thib-s/quadripod_robot/3d/mg996_base/exports/legA.stl

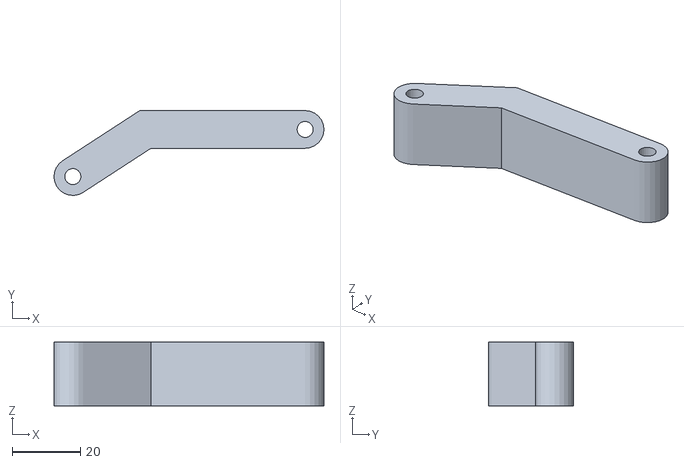
[picture p16: CAD file, 2018-07-05]
3d/mg996_base/exports/legA.stl
78.8 x 24.8 x 18.6
