thib-s/quadripod_robot/3d/hackaday_base/legA.stl

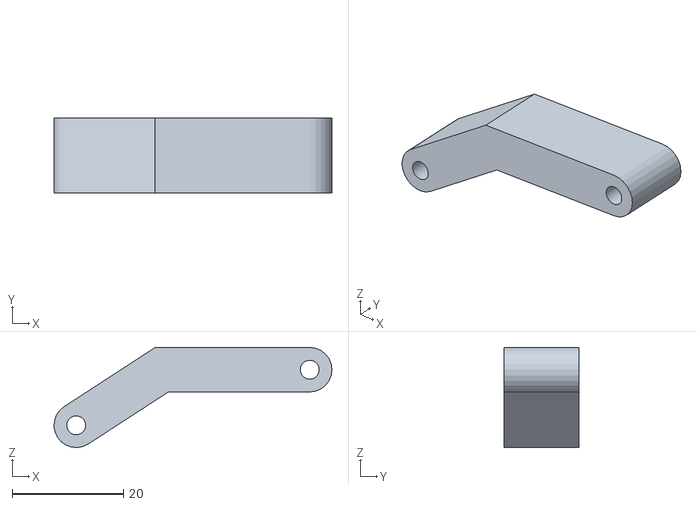
[picture p17: CAD file, 2018-07-05]
3d/hackaday_base/legA.stl
50.0 x 13.5 x 18.0
